mundodisco8/LED_Dimmer/firmware/Gruffalo_Dimmer/src/brightnessLUT.c

/**
 * @file brightnessLUT.c
 * @author Joel Santos (jsantosrico@gmail.com)
 * @brief Provides the definition of the gamma-corrected brightness look up table
 * @version 0.1
 * @date 2026-02-11
 *
 * @copyright Copyright (c) 2026
 *
 * This file is generated from the code on the \"PWM And Breathe Effect\" jupyter notebook in /docs
 *
 */

#include "brightnessLUT.h"

/**
 * @brief Contains the gamma-corrected brightness values, mapping percentage with two decimal places (as a uint) to the
 * compare register value required to obtain that perceived level of brightness
 *
 * Gamma-value -> 2.3
 *
 */
const uint32_t brightnessLookUp[GAMMA_LUT_SIZE] = {
    0,     0,     0,     0,     0,     0,     0,     0,     0,     0,     0,     0,     0,     0,     0,     0,
    0,     0,     0,     0,     0,     0,     0,     0,     0,     0,     0,     0,     0,     0,     0,     0,
    0,     0,     0,     0,     0,     0,     0,     0,     0,     0,     0,     0,     0,     0,     0,     0,
    0,     0,     0,     0,     0,     0,     0,     0,     0,     0,     0,     0,     0,     0,     0,     0,
    0,     0,     0,     0,     0,     0,     0,     0,     0,     0,     0,     0,     0,     0,     0,     0,
    0,     0,     0,     0,     0,     0,     0,     0,     0,     0,     0,     0,     0,     0,     0,     0,
    0,     0,     0,     0,     0,     0,     1,     1,     1,     1,     1,     1,     1,     1,     1,     1,
    1,     1,     1,     1,     1,     1,     1,     1,     1,     1,     1,     1,     1,     1,     1,     1,
    1,     1,     1,     1,     1,     1,     1,     1,     1,     1,     1,     1,     1,     1,     1,     1,
    1,     1,     1,     1,     1,     1,     1,     1,     1,     1,     1,     1,     1,     1,     1,     1,
    1,     1,     1,     1,     2,     2,     2,     2,     2,     2,     2,     2,     2,     2,     2,     2,
    2,     2,     2,     2,     2,     2,     2,     2,     2,     2,     2,     2,     2,     2,     2,     2,
    2,     2,     2,     2,     2,     2,     2,     2,     2,     2,     2,     2,     2,     3,     3,     3,
    3,     3,     3,     3,     3,     3,     3,     3,     3,     3,     3,     3,     3,     3,     3,     3,
    3,     3,     3,     3,     3,     3,     3,     3,     3,     3,     3,     3,     3,     4,     4,     4,
    4,     4,     4,     4,     4,     4,     4,     4,     4,     4,     4,     4,     4,     4,     4,     4,
    4,     4,     4,     4,     4,     4,     4,     4,     4,     5,     5,     5,     5,     5,     5,     5,
    5,     5,     5,     5,     5,     5,     5,     5,     5,     5,     5,     5,     5,     5,     5,     5,
    5,     6,     6,     6,     6,     6,     6,     6,     6,     6,     6,     6,     6,     6,     6,     6,
    6,     6,     6,     6,     6,     6,     7,     7,     7,     7,     7,     7,     7,     7,     7,     7,
    7,     7,     7,     7,     7,     7,     7,     7,     7,     7,     8,     8,     8,     8,     8,     8,
    8,     8,     8,     8,     8,     8,     8,     8,     8,     8,     8,     8,     8,     9,     9,     9,
    9,     9,     9,     9,     9,     9,     9,     9,     9,     9,     9,     9,     9,     9,     10,    10,
    10,    10,    10,    10,    10,    10,    10,    10,    10,    10,    10,    10,    10,    10,    11,    11,
    11,    11,    11,    11,    11,    11,    11,    11,    11,    11,    11,    11,    11,    11,    12,    12,
    12,    12,    12,    12,    12,    12,    12,    12,    12,    12,    12,    12,    13,    13,    13,    13,
    13,    13,    13,    13,    13,    13,    13,    13,    13,    13,    14,    14,    14,    14,    14,    14,
    14,    14,    14,    14,    14,    14,    14,    14,    15,    15,    15,    15,    15,    15,    15,    15,
    15,    15,    15,    15,    15,    16,    16,    16,    16,    16,    16,    16,    16,    16,    16,    16,
    16,    17,    17,    17,    17,    17,    17,    17,    17,    17,    17,    17,    17,    18,    18,    18,
    18,    18,    18,    18,    18,    18,    18,    18,    18,    19,    19,    19,    19,    19,    19,    19,
    19,    19,    19,    19,    20,    20,    20,    20,    20,    20,    20,    20,    20,    20,    20,    21,
    21,    21,    21,    21,    21,    21,    21,    21,    21,    21,    22,    22,    22,    22,    22,    22,
    22,    22,    22,    22,    23,    23,    23,    23,    23,    23,    23,    23,    23,    23,    24,    24,
    24,    24,    24,    24,    24,    24,    24,    24,    25,    25,    25,    25,    25,    25,    25,    25,
    25,    25,    26,    26,    26,    26,    26,    26,    26,    26,    26,    27,    27,    27,    27,    27,
    27,    27,    27,    27,    27,    28,    28,    28,    28,    28,    28,    28,    28,    28,    29,    29,
    29,    29,    29,    29,    29,    29,    29,    30,    30,    30,    30,    30,    30,    30,    30,    31,
    31,    31,    31,    31,    31,    31,    31,    31,    32,    32,    32,    32,    32,    32,    32,    32,
    33,    33,    33,    33,    33,    33,    33,    33,    33,    34,    34,    34,    34,    34,    34,    34,
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
