mundodisco8/LED_Dimmer/firmware/Gruffalo_Dimmer/autogen/sl_component_catalog.h

#ifndef SL_COMPONENT_CATALOG_H
#define SL_COMPONENT_CATALOG_H

// APIs present in project
#define SL_CATALOG_APP_ASSERT_PRESENT
#define SL_CATALOG_APP_LOG_PRESENT
#define SL_CATALOG_BGAPI_PROTOCOL_PRESENT
#define SL_CATALOG_BLUETOOTH_CONFIGURATION_PRESENT
#define SL_CATALOG_BLUETOOTH_CTE_SUPPORT_PRESENT
#define SL_CATALOG_BLUETOOTH_FEATURE_ADVERTISER_PRESENT
#define SL_CATALOG_BLUETOOTH_FEATURE_BUILTIN_BONDING_DATABASE_PRESENT
#define SL_CATALOG_BLUETOOTH_FEATURE_CONNECTION_PRESENT
#define SL_CATALOG_BLUETOOTH_FEATURE_CONNECTION_ROLE_CENTRAL_PRESENT
#define SL_CATALOG_BLUETOOTH_FEATURE_CONNECTION_ROLE_PERIPHERAL_PRESENT
#define SL_CATALOG_BLUETOOTH_FEATURE_GAP_PRESENT
#define SL_CATALOG_BLUETOOTH_FEATURE_GATT_PRESENT
#define SL_CATALOG_BLUETOOTH_FEATURE_GATT_SERVER_PRESENT
#define SL_CATALOG_BLUETOOTH_FEATURE_LEGACY_ADVERTISER_PRESENT
#define SL_CATALOG_BLUETOOTH_FEATURE_LEGACY_SCANNER_PRESENT
#define SL_CATALOG_BLUETOOTH_FEATURE_SCANNER_PRESENT
#define SL_CATALOG_BLUETOOTH_FEATURE_SM_PRESENT
#define SL_CATALOG_BLUETOOTH_FEATURE_SYSTEM_PRESENT
#define SL_CATALOG_BLUETOOTH_HOST_ADAPTATION_PRESENT
#define SL_CATALOG_BLUETOOTH_PRESENT
#define SL_CATALOG_CLOCK_MANAGER_PRESENT
#define SL_CATALOG_DEVICE_INIT_PRESENT
#define SL_CATALOG_DEVICE_INIT_DCDC_PRESENT
#define SL_CATALOG_EMLIB_CORE_PRESENT
#define SL_CATALOG_GATT_CONFIGURATION_PRESENT
#define SL_CATALOG_GPIO_PRESENT
#define SL_CATALOG_GPIOINTERRUPT_PRESENT
#define SL_CATALOG_HAL_SYSTEM_PRESENT
#define SL_CATALOG_INTERRUPT_MANAGER_PRESENT
#define SL_CATALOG_IOSTREAM_PRESENT
#define SL_CATALOG_IOSTREAM_EUSART_PRESENT
#define SL_CATALOG_RETARGET_STDIO_PRESENT
#define SL_CATALOG_IOSTREAM_UART_COMMON_PRESENT
#define SL_CATALOG_MEMORY_MANAGER_PRESENT
#define SL_CATALOG_MEMORY_PROFILER_API_PRESENT
#define SL_CATALOG_MPU_PRESENT
#define SL_CATALOG_NVM3_DEFAULT_PRESENT
#define SL_CATALOG_NVM3_PRESENT
#define SL_CATALOG_POWER_MANAGER_PRESENT
#define SL_CATALOG_POWER_MANAGER_DEEPSLEEP_BLOCKING_HFXO_RESTORE_PRESENT
#define SL_CATALOG_PSA_CRYPTO_PRESENT
#define SL_CATALOG_RAIL_LIB_PRESENT
#define SL_CATALOG_SE_MANAGER_PRESENT
#define SL_CATALOG_SL_CORE_PRESENT
#define SL_CATALOG_SL_MAIN_PRESENT
#define SL_CATALOG_CUSTOM_MAIN_PRESENT
#define SL_CATALOG_SL_RAIL_UTIL_BUILT_IN_PHYS_PRESENT
#define SL_CATALOG_RAIL_UTIL_BUILT_IN_PHYS_PRESENT
#define SL_CATALOG_SL_RAIL_UTIL_COMPATIBLE_PA_PRESENT
#define SL_CATALOG_SL_RAIL_UTIL_POWER_MANAGER_INIT_PRESENT
#define SL_CATALOG_RAIL_UTIL_POWER_MANAGER_INIT_PRESENT
#define SL_CATALOG_SL_RAIL_UTIL_PTI_PRESENT
#define SL_CATALOG_RAIL_UTIL_PTI_PRESENT
#define SL_CATALOG_SL_SYSTEM_COMPATIBILITY_PRESENT
#define SL_CATALOG_SLEEPTIMER_PRESENT
#define SL_CATALOG_SLI_PROTOCOL_CRYPTO_PRESENT

#endif // SL_COMPONENT_CATALOG_H
