mundodisco8/LED_Dimmer/firmware/test/test/test_buttonActions.c

#include <unity.h>

// Module being tested
#include "buttonActions.h"

// Mocks and others
#include "app_log.h"
#include "mock_LEDIndicator.h"
#include "mock_PWMControl.h"
#include "mock_buttons.h"
#include "mock_debounce.h"
#include "mock_effectControl.h"
#include "mock_gpio_HW.h"
#include "mock_sleepyTimers_HW.h"

/*
 * Unit tests for "buttoyActions.h"
 */

// externs to test some static variables in the module
extern uint8_t channelIdx;
extern const uint32_t BRIGHTNESS_DELTA;  // in percent with two decimals -> 5%

// Provide values for some globals whose definitions are lost when using mocks
const uint32_t PWM_FREQUENCY         = 1000UL;
const uint32_t BREATHE_MIN_PERIOD_MS = BREATHE_LUT_SIZE;

void setUp(void) {
    // reset globals
    channelIdx = 0;
}

void tearDown(void) {}

// gpioCallbackButton
// The press of a button starts the debounce and sample timers
void test_gpioCallBackButton(void) {
    button_t testButton = {0};
    uint8_t testIntNo   = 4;
    // Set Expectations
    startButtonTimer_ExpectAndReturn(&testButton, TIMER_LONGPRESS, BTN_OK);
    startButtonTimer_ExpectAndReturn(&testButton, TIMER_SAMPLE, BTN_OK);

    gpioCallbackButton(testIntNo, &testButton);
}

// gpioCallbackQuad
// Quad input is simpler, as it has HW debouncing. we just check if we are rotating CW or CCW
// The quad encoder object is passed as context
// We will need two dummy callback functions to test them
uint32_t quadCallbackTest = 0;
void dummy_CWAction(void* ctx) {
    (void)ctx;
    quadCallbackTest = 1;
}

void dummy_CCWAction(void* ctx) {
    (void)ctx;
    quadCallbackTest = 2;
}

void test_gpioCallBackQuad(void) {
    uint32_t testIntNo         = 9;
    pinPort_t testPort         = portA;
    uint8_t testPinNo          = 4;
    quad_encoder_t testEncoder = {.pin1No                 = testPinNo,
                                  .pin1Port               = testPort,
                                  .clockWiseAction        = dummy_CWAction,
                                  .counterClockWiseAction = dummy_CCWAction};

    // Set Expectations - CW rotation
    readPin_ExpectAndReturn(testEncoder.pin1Port, testEncoder.pin1No, 1);

    gpioCallbackQuad(testIntNo, &testEncoder);
    TEST_ASSERT_EQUAL(1, quadCallbackTest);

    // Test 2 - CCW rotation - Set Expectations
    readPin_ExpectAndReturn(testEncoder.pin1Port, testEncoder.pin1No, 0);

    gpioCallbackQuad(testIntNo, &testEncoder);
    TEST_ASSERT_EQUAL(2, quadCallbackTest);
}

// button0 changes the current PWM channel active. Third press resets channel to 0
void test_button0ReleasedAfterShortPress(void) {
    LEDChannel_t testChannel = LED_CHANNEL_1;
    button_t testBtn         = {.prevState = BUTTON_PRESSED};  // So all releases will be "short" releases
    channelIdx               = (uint32_t)testChannel;

    // Set Expectations - 1st press, switch to ch2
    LEDChannel_t expectedCh     = LED_CHANNEL_2;
    channel_t expectedIndicator = CHANNEL_2;
    LEDIndicator_setChannel_Expect(expectedIndicator);

    button0Released(&testBtn);
    TEST_ASSERT_EQUAL(expectedCh, channelIdx);

    // Second press gets channel 3
    expectedCh        = LED_CHANNEL_3;
    expectedIndicator = CHANNEL_3;
    LEDIndicator_setChannel_Expect(expectedIndicator);

    // Set Expectations
    button0Released(&testBtn);
    TEST_ASSERT_EQUAL(expectedCh, channelIdx);

    // Third press sets to ALL
    expectedCh        = LED_CHANNELS_ALL;
    expectedIndicator = CHANNEL_ALL;
    LEDIndicator_setChannel_Expect(expectedIndicator);

    // Set Expectations
    button0Released(&testBtn);
    TEST_ASSERT_EQUAL(expectedCh, channelIdx);

    // And fourth resets back to channel 1
    expectedCh        = LED_CHANNEL_1;
    expectedIndicator = CHANNEL_1;

    // Set Expectations
    LEDIndicator_setChannel_Expect(expectedIndicator);

    button0Released(&testBtn);
    TEST_ASSERT_EQUAL(expectedCh, channelIdx);
}

// button0 on long press. does nothing, for now
void test_button0ReleasedAfterLongPress(void) {
    button_t testBtn = {.prevState = BUTTON_LONGPRESSED};  // So the release will be a "long" release

    // No action on long release

    button0Released(&testBtn);
}

// Button 0 ShortPressed does nothing for now
void test_button0ShortPressed(void) { button0ShortPressed(NULL); }

// Button 0 LongPressed does nothing for now
void test_button0LongPressed(void) { button0LongPressed(NULL); }

// Test Quad actions
// Rotating CW increases channel's % by 5, and CCW decreases it
// Rotating while any press rises/lowers all channels

void test_quad0ClockWise_SingleChannelSuccess(void) {
    uint32_t expectedInitialBrightness = 1000;
    uint32_t expectedFinalBrightness   = expectedInitialBrightness + BRIGHTNESS_DELTA;
    LEDChannel_t expectedChannel       = LED_CHANNEL_1;

    // Set Expectations
    getLEDBrightness_ExpectAndReturn(expectedChannel, expectedInitialBrightness);
    setLEDBrightness_ExpectAndReturn(expectedChannel, expectedFinalBrightness, EFF_OK);
    quad0ClockWise(NULL);

    // Turn twice more...
    expectedFinalBrightness = expectedInitialBrightness + (3 * BRIGHTNESS_DELTA);

    // Set Expectations
    getLEDBrightness_ExpectAndReturn(expectedChannel, expectedInitialBrightness + BRIGHTNESS_DELTA);
    setLEDBrightness_ExpectAndReturn(expectedChannel, expectedInitialBrightness + (2 * BRIGHTNESS_DELTA), EFF_OK);
    getLEDBrightness_ExpectAndReturn(expectedChannel, expectedInitialBrightness + (2 * BRIGHTNESS_DELTA));
    setLEDBrightness_ExpectAndReturn(expectedChannel, expectedFinalBrightness, EFF_OK);
    quad0ClockWise(NULL);
    quad0ClockWise(NULL);
}

void test_quad0ClockWise_SingleChannelMaxBrightness(void) {
    uint32_t expectedInitialBrightness = MAX_BRIGHTNESS;
    LEDChannel_t expectedChannel       = LED_CHANNEL_1;

    // Set Expectations
    getLEDBrightness_ExpectAndReturn(expectedChannel, expectedInitialBrightness);

    quad0ClockWise(NULL);
}

void test_quad0ClockWise_AllChannelsPressed(void) {
    uint32_t testBrightnessCh1 = 1000;
    uint32_t testBrightnessCh2 = 2000;
    uint32_t testBrightnessCh3 = 3000;
    LEDChannel_t testChannel   = LED_CHANNELS_ALL;
    channelIdx                 = (uint32_t)testChannel;

    // Set Expectations
    uint32_t expectedBirghtnessCh1 = testBrightnessCh1 + BRIGHTNESS_DELTA;
    uint32_t expectedBirghtnessCh2 = testBrightnessCh2 + BRIGHTNESS_DELTA;
    uint32_t expectedBirghtnessCh3 = testBrightnessCh3 + BRIGHTNESS_DELTA;

    getLEDBrightness_ExpectAndReturn(LED_CHANNEL_1, testBrightnessCh1);
    setLEDBrightness_ExpectAndReturn(LED_CHANNEL_1, expectedBirghtnessCh1, EFF_OK);
    getLEDBrightness_ExpectAndReturn(LED_CHANNEL_2, testBrightnessCh2);
    setLEDBrightness_ExpectAndReturn(LED_CHANNEL_2, expectedBirghtnessCh2, EFF_OK);
    getLEDBrightness_ExpectAndReturn(LED_CHANNEL_3, testBrightnessCh3);
    setLEDBrightness_ExpectAndReturn(LED_CHANNEL_3, expectedBirghtnessCh3, EFF_OK);

    quad0ClockWise(NULL);
}

void test_quad0CounterClockWise_SingleChannelSuccess(void) {
    uint32_t expectedInitialBrightness = 9000;
    uint32_t expectedFinalBrightness   = expectedInitialBrightness - BRIGHTNESS_DELTA;
    LEDChannel_t expectedChannel       = LED_CHANNEL_1;

    // Set Expectations
    getLEDBrightness_ExpectAndReturn(expectedChannel, expectedInitialBrightness);
    setLEDBrightness_ExpectAndReturn(expectedChannel, expectedFinalBrightness, EFF_OK);
    quad0CounterClockWise(NULL);

    // Turn twice more...
    expectedFinalBrightness = expectedInitialBrightness - (3 * BRIGHTNESS_DELTA);

    // Set Expectations
    getLEDBrightness_ExpectAndReturn(expectedChannel, expectedInitialBrightness - BRIGHTNESS_DELTA);
    setLEDBrightness_ExpectAndReturn(expectedChannel, expectedInitialBrightness - (2 * BRIGHTNESS_DELTA), EFF_OK);
    getLEDBrightness_ExpectAndReturn(expectedChannel, expectedInitialBrightness - (2 * BRIGHTNESS_DELTA));
    setLEDBrightness_ExpectAndReturn(expectedChannel, expectedFinalBrightness, EFF_OK);
    quad0CounterClockWise(NULL);
    quad0CounterClockWise(NULL);
}

void test_quad0CounterClockWise_SingleChannelMinBrightness(void) {
    uint32_t expectedInitialBrightness = MIN_BRIGHTNESS;
    LEDChannel_t expectedChannel       = LED_CHANNEL_1;

    // Set Expectations
    getLEDBrightness_ExpectAndReturn(expectedChannel, expectedInitialBrightness);

    quad0CounterClockWise(NULL);
}

void test_quad0CounterClockWise_AllChannelsPressed(void) {
    uint32_t testBrightnessCh1 = 1000;
    uint32_t testBrightnessCh2 = 2000;
    uint32_t testBrightnessCh3 = 3000;
    LEDChannel_t testChannel   = LED_CHANNELS_ALL;
    channelIdx                 = (uint32_t)testChannel;

    // Set Expectations
    uint32_t expectedBirghtnessCh1 = testBrightnessCh1 - BRIGHTNESS_DELTA;
    uint32_t expectedBirghtnessCh2 = testBrightnessCh2 - BRIGHTNESS_DELTA;
    uint32_t expectedBirghtnessCh3 = testBrightnessCh3 - BRIGHTNESS_DELTA;

    getLEDBrightness_ExpectAndReturn(LED_CHANNEL_1, testBrightnessCh1);
    setLEDBrightness_ExpectAndReturn(LED_CHANNEL_1, expectedBirghtnessCh1, EFF_OK);
    getLEDBrightness_ExpectAndReturn(LED_CHANNEL_2, testBrightnessCh2);
    setLEDBrightness_ExpectAndReturn(LED_CHANNEL_2, expectedBirghtnessCh2, EFF_OK);
    getLEDBrightness_ExpectAndReturn(LED_CHANNEL_3, testBrightnessCh3);
    setLEDBrightness_ExpectAndReturn(LED_CHANNEL_3, expectedBirghtnessCh3, EFF_OK);

    quad0CounterClockWise(NULL);
}

/**
 * button1Released
 * - Shortpress changes from fixed to breathe
 * - Shortpress changes from breathe to fixed
 */

void test_button1Released_FixedToBreathe(void) {
    // Shortpress, current lastPressMs is 0
    button_t testBtn = {
        .prevState = BUTTON_PRESSED  // so release is "short" release
    };
    LEDChannel_t testChannel    = LED_CHANNEL_1;
    anim_t testCurrAnimation    = ANIM_FIXED;
    anim_t expectedNewAnimation = ANIM_BREATHE;
    channelIdx                  = testChannel;

    // Set Expectations
    getAnimation_ExpectAndReturn(testChannel, testCurrAnimation);
    setAnimation_ExpectAndReturn(testChannel, expectedNewAnimation, EFF_OK);
    getEffectName_ExpectAndReturn(expectedNewAnimation, "Breathe Effect");

    button1Released(&testBtn);
}

void test_button1Released_BreatheToFixed(void) {
    // Shortpress, current lastPressMs is 0
    button_t testBtn = {
        .prevState = BUTTON_PRESSED  // so release is "short" release
    };
    LEDChannel_t testChannel    = LED_CHANNEL_1;
    anim_t testCurrAnimation    = ANIM_BREATHE;
    anim_t expectedNewAnimation = ANIM_FIXED;
    channelIdx                  = testChannel;

    // Set Expectations
    getAnimation_ExpectAndReturn(testChannel, testCurrAnimation);
    setAnimation_ExpectAndReturn(testChannel, expectedNewAnimation, EFF_OK);
    getEffectName_ExpectAndReturn(expectedNewAnimation, "Fixed Brightness");

    button1Released(&testBtn);
}

void test_button1Released_AllChannelsFixedToBreathe(void) {
    // Shortpress, current lastPressMs is 0
    button_t testBtn = {
        .prevState = BUTTON_PRESSED  // so release is "short" release
    };
    LEDChannel_t testChannel    = LED_CHANNELS_ALL;
    anim_t testCurrAnimation    = ANIM_FIXED;
    anim_t expectedNewAnimation = ANIM_BREATHE;
    channelIdx                  = testChannel;

    // Set Expectations
    LEDChannel_t expectedChannelGetEffect = LED_CHANNEL_1;
    getAnimation_ExpectAndReturn(expectedChannelGetEffect, testCurrAnimation);
    setAnimation_ExpectAndReturn(LED_CHANNEL_1, expectedNewAnimation, EFF_OK);
    setAnimation_ExpectAndReturn(LED_CHANNEL_2, expectedNewAnimation, EFF_OK);
    setAnimation_ExpectAndReturn(LED_CHANNEL_3, expectedNewAnimation, EFF_OK);
    getEffectName_ExpectAndReturn(expectedNewAnimation, "Breathe Effect");

    button1Released(&testBtn);
}

// button0 on long press. does nothing, for now
void test_button1Released_LongPress(void) {
    button_t testBtn = {
        .prevState = BUTTON_LONGPRESSED  // so release is "short" release
    };

    // No action on long release

    button1Released(&testBtn);
}

// Button 1 Pressed does nothing for now
void test_button1Pressed(void) { button1ShortPressed(NULL); }

// Button 1 LongPressed does nothing for now
void test_button1LongPressed(void) { button1LongPressed(NULL); }

/**
 * quad1Clockwise
 *
 */

void test_quad1Clockwise_IncreaseBreathePeriod_SingleChannelSuccess(void) {
    uint32_t currentPeriod       = 1000;
    LEDChannel_t expectedChannel = LED_CHANNEL_1;

    uint32_t expectedPeriod = currentPeriod + (BREATHE_LUT_SIZE * 1000UL / PWM_FREQUENCY);

    // Set expecations
    getBreathePeriod_ExpectAndReturn(expectedChannel, currentPeriod);
    setBreathePeriod_ExpectAndReturn(expectedChannel, expectedPeriod, EFF_OK);

    quad1ClockWise(NULL);
}

void test_quad1ClockWise_AllChannelsPressed(void) {
    uint32_t testPeriodCh1           = 1000;
    uint32_t testPeriodCh2           = 2000;
    uint32_t testPeriodCh3           = 3000;
    LEDChannel_t testChannel         = LED_CHANNELS_ALL;
    channelIdx                       = (uint32_t)testChannel;
    uint32_t BREATHE_PERIOD_MS_DELTA = BREATHE_LUT_SIZE * 1000UL / PWM_FREQUENCY;

    // Set Expectations
    uint32_t expectedPeriodCh1 = testPeriodCh1 + BREATHE_PERIOD_MS_DELTA;
    uint32_t expectedPeriodCh2 = testPeriodCh2 + BREATHE_PERIOD_MS_DELTA;
    uint32_t expectedPeriodCh3 = testPeriodCh3 + BREATHE_PERIOD_MS_DELTA;

    getBreathePeriod_ExpectAndReturn(LED_CHANNEL_1, testPeriodCh1);
    setBreathePeriod_ExpectAndReturn(LED_CHANNEL_1, expectedPeriodCh1, EFF_OK);
    getBreathePeriod_ExpectAndReturn(LED_CHANNEL_2, testPeriodCh2);
    setBreathePeriod_ExpectAndReturn(LED_CHANNEL_2, expectedPeriodCh2, EFF_OK);
    getBreathePeriod_ExpectAndReturn(LED_CHANNEL_3, testPeriodCh3);
    setBreathePeriod_ExpectAndReturn(LED_CHANNEL_3, expectedPeriodCh3, EFF_OK);

    quad1ClockWise(NULL);
}

/**
 * quad1CounterClockwise
 *
 */

void test_quad1CounterClockwise_DecreaseBreathePeriod_SingleChannel(void) {
    uint32_t currentPeriod       = 1000;
    LEDChannel_t expectedChannel = LED_CHANNEL_1;

    uint32_t expectedPeriod = currentPeriod - (BREATHE_LUT_SIZE * 1000UL / PWM_FREQUENCY);

    // Set expecations
    getBreathePeriod_ExpectAndReturn(expectedChannel, currentPeriod);
    setBreathePeriod_ExpectAndReturn(expectedChannel, expectedPeriod, EFF_OK);

    quad1CounterClockWise(NULL);
}

void test_quad1CounterClockwise_DontGoBelowMinimum_SingleChannel(void) {
    uint32_t currentPeriod       = BREATHE_MIN_PERIOD_MS;
    LEDChannel_t expectedChannel = LED_CHANNEL_1;

    uint32_t expectedPeriod = BREATHE_MIN_PERIOD_MS;

    // Set expecations
    getBreathePeriod_ExpectAndReturn(expectedChannel, currentPeriod);
    setBreathePeriod_ExpectAndReturn(expectedChannel, expectedPeriod, EFF_OK);

    quad1CounterClockWise(NULL);
}

void test_quad1CounterClockWise_AllChannelsPressed(void) {
    uint32_t testPeriodCh1           = 1000;
    uint32_t testPeriodCh2           = 2000;
    uint32_t testPeriodCh3           = 3000;
    LEDChannel_t testChannel         = LED_CHANNELS_ALL;
    channelIdx                       = (uint32_t)testChannel;
    uint32_t BREATHE_PERIOD_MS_DELTA = -(BREATHE_LUT_SIZE * 1000UL / PWM_FREQUENCY);

    // Set Expectations
    uint32_t expectedPeriodCh1 = testPeriodCh1 + BREATHE_PERIOD_MS_DELTA;
    uint32_t expectedPeriodCh2 = testPeriodCh2 + BREATHE_PERIOD_MS_DELTA;
    uint32_t expectedPeriodCh3 = testPeriodCh3 + BREATHE_PERIOD_MS_DELTA;

    getBreathePeriod_ExpectAndReturn(LED_CHANNEL_1, testPeriodCh1);
    setBreathePeriod_ExpectAndReturn(LED_CHANNEL_1, expectedPeriodCh1, EFF_OK);
    getBreathePeriod_ExpectAndReturn(LED_CHANNEL_2, testPeriodCh2);
    setBreathePeriod_ExpectAndReturn(LED_CHANNEL_2, expectedPeriodCh2, EFF_OK);
    getBreathePeriod_ExpectAndReturn(LED_CHANNEL_3, testPeriodCh3);
    setBreathePeriod_ExpectAndReturn(LED_CHANNEL_3, expectedPeriodCh3, EFF_OK);

    quad1CounterClockWise(NULL);
}
